csinko/io-master/PDF/PCB - Silkscreen.pdf

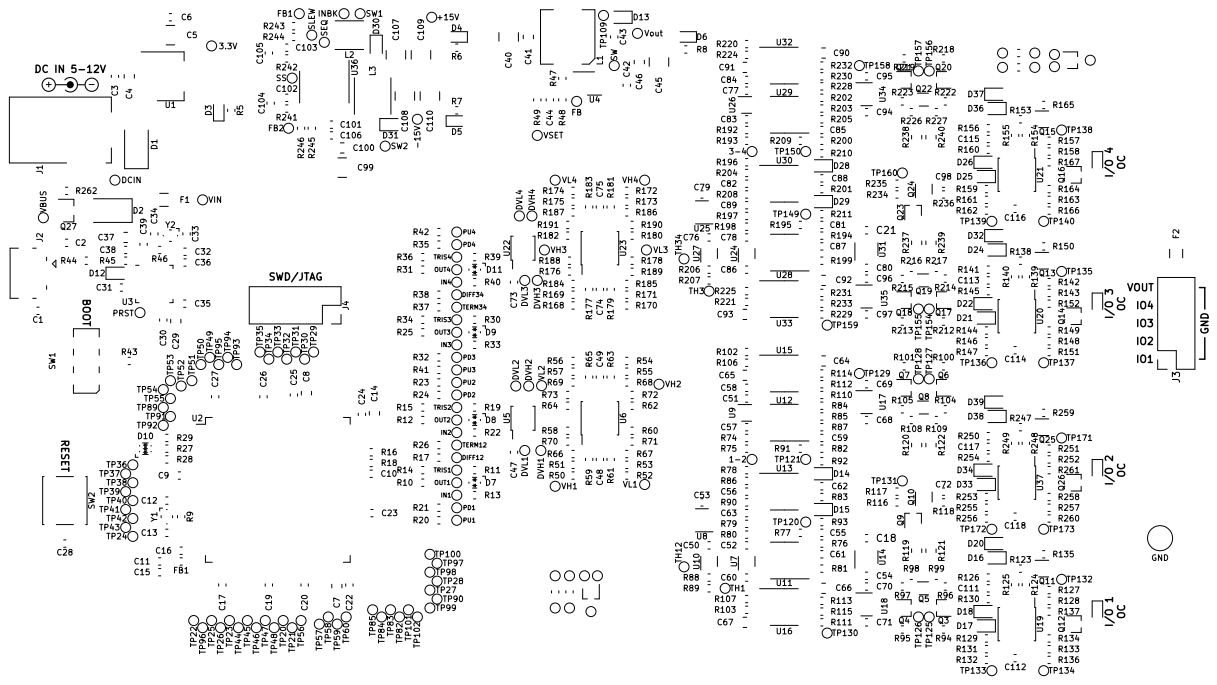
[picture p24: page 1]

DT18 - I/O MASTER
File: io-master.kicad_pcb Sheet: THE UNIVERSITY OF AKRON
