csinko/io-master/PDF/PCB - Top Copper.pdf

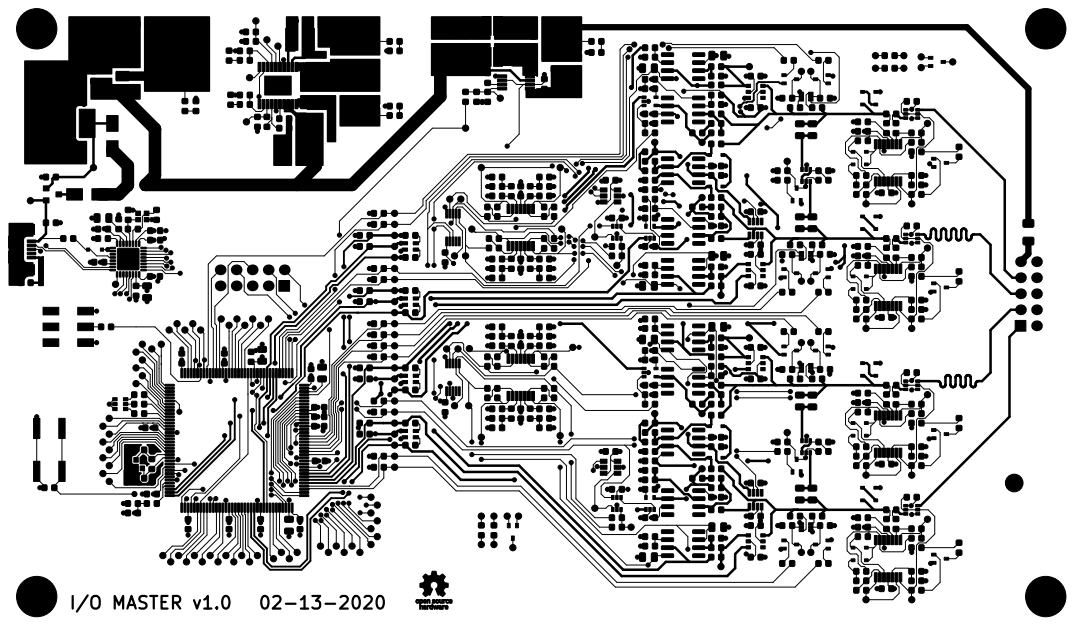
[picture p25: page 1]

DT18 - I/O MASTER
File: io-master.kicad_pcb Sheet: THE UNIVERSITY OF AKRON
