csinko/io-master/mcu/io_master/mcu/stm32h743/src/clock.c

#include "clock.h"
#include <stdint.h>
#include <unistd.h>
#include "stm32h7xx_hal.h"
#include "stm32h743xx.h"

IOM_ERROR InitSystemClock(void) {
  RCC_OscInitTypeDef RCC_OscInitStruct = {0};
  RCC_ClkInitTypeDef RCC_ClkInitStruct = {0};

  HAL_PWREx_ConfigSupply(PWR_LDO_SUPPLY);

  __HAL_PWR_VOLTAGESCALING_CONFIG(PWR_REGULATOR_VOLTAGE_SCALE0);

  while(!__HAL_PWR_GET_FLAG(PWR_FLAG_VOSRDY)) {}

RCC_OscInitStruct.OscillatorType = RCC_OSCILLATORTYPE_HSI | RCC_OSCILLATORTYPE_HSE;
  RCC_OscInitStruct.HSEState = RCC_HSE_BYPASS;
  RCC_OscInitStruct.HSIState = RCC_HSI_DIV1;
  RCC_OscInitStruct.HSICalibrationValue = RCC_HSICALIBRATION_DEFAULT;
  RCC_OscInitStruct.PLL.PLLState = RCC_PLL_ON;
  RCC_OscInitStruct.PLL.PLLSource = RCC_PLLSOURCE_HSE;

  RCC_OscInitStruct.PLL.PLLM = 8;
  RCC_OscInitStruct.PLL.PLLN = 160;
  RCC_OscInitStruct.PLL.PLLFRACN = 0;
  RCC_OscInitStruct.PLL.PLLP = 2;
  RCC_OscInitStruct.PLL.PLLR = 2;
  RCC_OscInitStruct.PLL.PLLQ = 4;

  RCC_OscInitStruct.PLL.PLLVCOSEL = RCC_PLL1VCOWIDE;
  RCC_OscInitStruct.PLL.PLLRGE = RCC_PLL1VCIRANGE_2;
  HAL_RCC_OscConfig(&RCC_OscInitStruct);

  RCC_ClkInitStruct.ClockType = (RCC_CLOCKTYPE_SYSCLK | RCC_CLOCKTYPE_HCLK | RCC_CLOCKTYPE_D1PCLK1 | RCC_CLOCKTYPE_PCLK1 | 
                                 RCC_CLOCKTYPE_PCLK2  | RCC_CLOCKTYPE_D3PCLK1);

  RCC_ClkInitStruct.SYSCLKSource = RCC_SYSCLKSOURCE_PLLCLK;
  RCC_ClkInitStruct.SYSCLKDivider = RCC_SYSCLK_DIV1;
  RCC_ClkInitStruct.AHBCLKDivider = RCC_HCLK_DIV2;
  RCC_ClkInitStruct.APB3CLKDivider = RCC_APB3_DIV2;  
  RCC_ClkInitStruct.APB1CLKDivider = RCC_APB1_DIV2; 
  RCC_ClkInitStruct.APB2CLKDivider = RCC_APB2_DIV2; 
  RCC_ClkInitStruct.APB4CLKDivider = RCC_APB4_DIV2; 
  HAL_RCC_ClockConfig(&RCC_ClkInitStruct, FLASH_LATENCY_4);


  RCC_PeriphCLKInitTypeDef PeriphClkInitStruct = {0};

  PeriphClkInitStruct.PeriphClockSelection = RCC_PERIPHCLK_USART3|RCC_PERIPHCLK_I2C3;
  PeriphClkInitStruct.Usart234578ClockSelection = RCC_USART234578CLKSOURCE_D2PCLK1;
  PeriphClkInitStruct.I2c123ClockSelection = RCC_I2C123CLKSOURCE_HSI;
  if (HAL_RCCEx_PeriphCLKConfig(&PeriphClkInitStruct) != HAL_OK)
  {
   return IOM_ERROR_INTERFACE; 
  }



  return IOM_OK;
}
