csinko/io-master/mcu/io_master/inc/io_dma.h

#ifndef __IO_MASTER_IO_DMA_H
#define __IO_MASTER_IO_DMA_H

#ifdef __cplusplus
extern "C" {
#endif

#include "core.h"
#include "stm32h7xx_hal.h"

DMA_HandleTypeDef hdma_dma_generator0;


IOM_ERROR InitDMA(void);
void StartDMATransfer(IOM_Output_Buffer* pBuffer);
void ResetDMA();

#ifdef __cplusplus
}
#endif
#endif
