csinko/io-master/mcu/io_master/inc/log.h

#ifndef __IOM_LOG_H_
#define __IOM_LOG_H_

#ifdef __cplusplus
extern "C" {
#endif


/// 
/// @brief logs a message
///
/// @param msg the message to log
///
void IOMLog(const char* msg);

#ifdef __cplusplus
}
#endif

#endif
