csinko/io-master/mcu/io_master/mcu/stm32h743/src/timer.c

#include "timer.h"
#include "stm32h743xx.h"
#include "stm32h7xx_hal.h"

IOM_ERROR InitTimers(void) {
  TIM_MasterConfigTypeDef sMasterConfig = {0};
  TIM_OC_InitTypeDef sConfigOC = {0};
  TIM_BreakDeadTimeConfigTypeDef sBreakDeadTimeConfig = {0};

  htim8.Instance = TIM8;
  TIM8->BDTR |= TIM_BDTR_MOE;
  htim8.Init.Prescaler = 0;
  htim8.Init.CounterMode = TIM_COUNTERMODE_UP;
  htim8.Init.Period = 1;
  htim8.Init.ClockDivision = TIM_CLOCKDIVISION_DIV1;
  htim8.Init.RepetitionCounter = 0;
  htim8.Init.AutoReloadPreload = TIM_AUTORELOAD_PRELOAD_DISABLE;
  if (HAL_TIM_PWM_Init(&htim8) != HAL_OK)
  {
    return IOM_ERROR_INVALID; //TODO put a better error here
  }
  TIM8->BDTR |= TIM_BDTR_MOE;
  sMasterConfig.MasterOutputTrigger = TIM_TRGO_RESET;
  sMasterConfig.MasterSlaveMode = TIM_MASTERSLAVEMODE_DISABLE;
  HAL_TIMEx_MasterConfigSynchronization(&htim8, &sMasterConfig); 


  sConfigOC.OCMode = TIM_OCMODE_PWM1;
  sConfigOC.Pulse = 1;
  sConfigOC.OCPolarity = TIM_OCPOLARITY_HIGH;
  sConfigOC.OCNPolarity = TIM_OCNPOLARITY_LOW;
  sConfigOC.OCFastMode = TIM_OCFAST_DISABLE;
  sConfigOC.OCIdleState = TIM_OCIDLESTATE_RESET;
  sConfigOC.OCNIdleState = TIM_OCNIDLESTATE_RESET;
  if (HAL_TIM_PWM_ConfigChannel(&htim8, &sConfigOC, TIM_CHANNEL_1) != HAL_OK)
  {
    return IOM_ERROR_INVALID; //TODO put a better error here
  }
  sConfigOC.Pulse = 1;
  if (HAL_TIM_PWM_ConfigChannel(&htim8, &sConfigOC, TIM_CHANNEL_3) != HAL_OK)
  {
    return IOM_ERROR_INVALID; //TODO put a better error here
  }
  sConfigOC.Pulse = 1;
  if (HAL_TIM_PWM_ConfigChannel(&htim8, &sConfigOC, TIM_CHANNEL_4) != HAL_OK)
  {
    return IOM_ERROR_INVALID; //TODO put a better error here
  }

  TIM8->BDTR |= TIM_BDTR_MOE;

  sBreakDeadTimeConfig.OffStateRunMode = TIM_OSSR_DISABLE;
  sBreakDeadTimeConfig.OffStateIDLEMode = TIM_OSSI_DISABLE;
  sBreakDeadTimeConfig.LockLevel = TIM_LOCKLEVEL_OFF;
  sBreakDeadTimeConfig.DeadTime = 0;
  sBreakDeadTimeConfig.BreakState = TIM_BREAK_DISABLE;
  sBreakDeadTimeConfig.BreakPolarity = TIM_BREAKPOLARITY_HIGH;
  sBreakDeadTimeConfig.AutomaticOutput = TIM_AUTOMATICOUTPUT_ENABLE;
  HAL_TIMEx_ConfigBreakDeadTime(&htim8, &sBreakDeadTimeConfig);

  //HAL_TIM_MspPostInit(&htim8); //TODO make this work
  TIM8->BDTR |= TIM_BDTR_MOE;

  if (HAL_TIM_PWM_Start(&htim8, TIM_CHANNEL_1) != HAL_OK) {
    return IOM_ERROR_INVALID; //TODO put a better error here
  }
  if (HAL_TIM_PWM_Start(&htim8, TIM_CHANNEL_3) != HAL_OK) {
    return IOM_ERROR_INVALID; //TODO put a better error here
  }
  if (HAL_TIM_PWM_Start(&htim8, TIM_CHANNEL_4) != HAL_OK) {
    return IOM_ERROR_INVALID; //TODO put a better error here
  }
    TIM8->BDTR |= TIM_BDTR_MOE;
    return IOM_OK;
}
