csinko/io-master/mcu/io_master/mcu/stm32h743/src/usb.c

#include "usb.h"
#include "core.h"

#include "usbd_core.h"
#include "usbd_desc.h"
#include "usbd_cdc.h"
#include "usbd_cdc_if.h"

#include "stm32h7xx.h"
#include "stm32h7xx_hal.h"

USBD_HandleTypeDef hUsbDeviceFS = {0};

IOM_ERROR InitUSB(void) {
  if (USBD_Init(&hUsbDeviceFS, &FS_Desc, DEVICE_FS) != USBD_OK)
  {
    Error_Handler();
  }
  if (USBD_RegisterClass(&hUsbDeviceFS, &USBD_CDC) != USBD_OK)
  {
    Error_Handler();
  }
  if (USBD_CDC_RegisterInterface(&hUsbDeviceFS, &USBD_Interface_fops_FS) != USBD_OK)
  {
    Error_Handler();
  }
  if (USBD_Start(&hUsbDeviceFS) != USBD_OK)
  {
    Error_Handler();
  }
  HAL_PWREx_EnableUSBVoltageDetector();
    return IOM_OK;
}
